duvohuu/Mechatronics-System-Design/Report/pictures/chapter5/c5_p3_Sub2.png

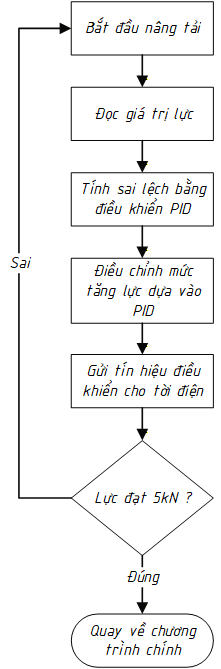
Report/pictures/chapter5/c5_p3_Sub2.png
